opinau/cv-2/modul 1 - openmv/Dokumentacija/images_sa_artifektima_cons_level/slika_1_off.bmp

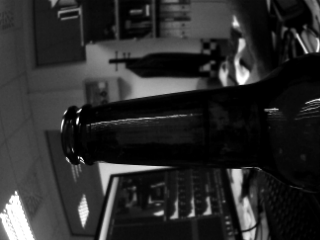
modul 1 - openmv/Dokumentacija/images_sa_artifektima_cons_level/slika_1_off.bmp
