opinau/cv-2/modul 1 - openmv/Kodovi/kicad_nacrt/openmv_breakout/openmv_breakout.jpg

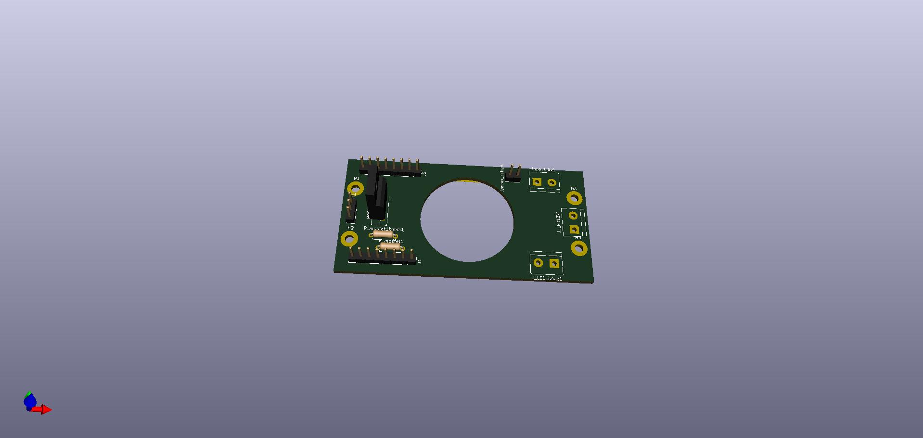
modul 1 - openmv/Kodovi/kicad_nacrt/openmv_breakout/openmv_breakout.jpg
