opinau/cv-2/modul 2 - rpi/Dokumentacija/last_frame.jpg

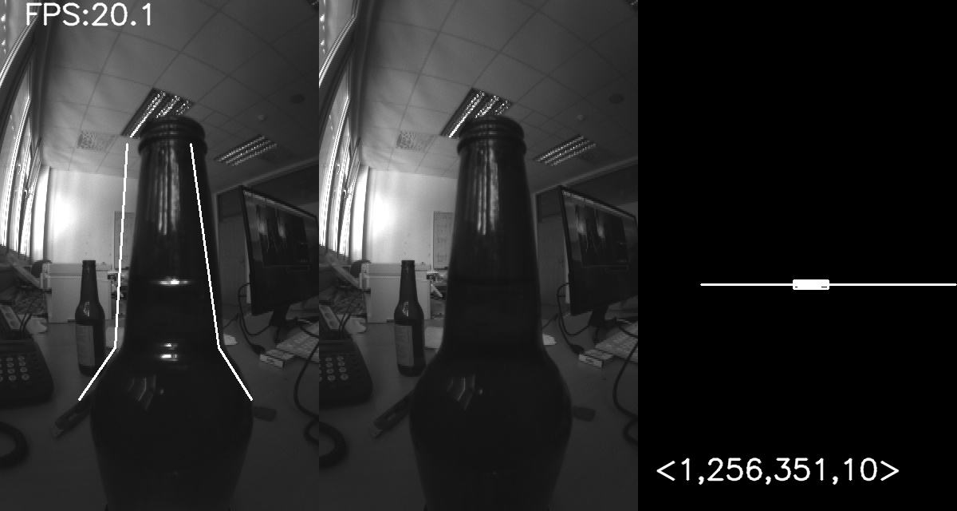
modul 2 - rpi/Dokumentacija/last_frame.jpg
