opinau/cv-2/modul 2 - rpi/Kodovi/fill_level/maska_rpi.bmp

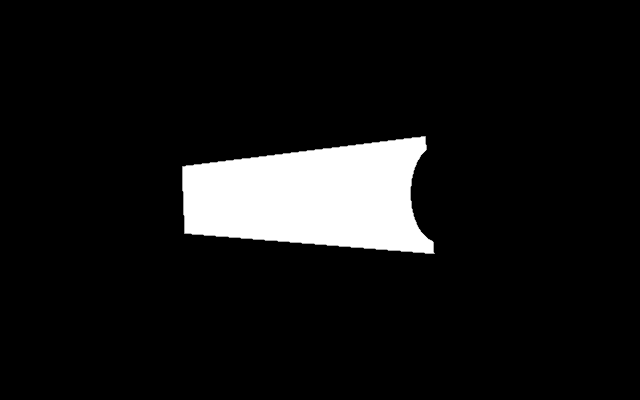
modul 2 - rpi/Kodovi/fill_level/maska_rpi.bmp
