opinau/cv-2/modul 2 - rpi/Kodovi/fill_level/slika_za_masku.bmp

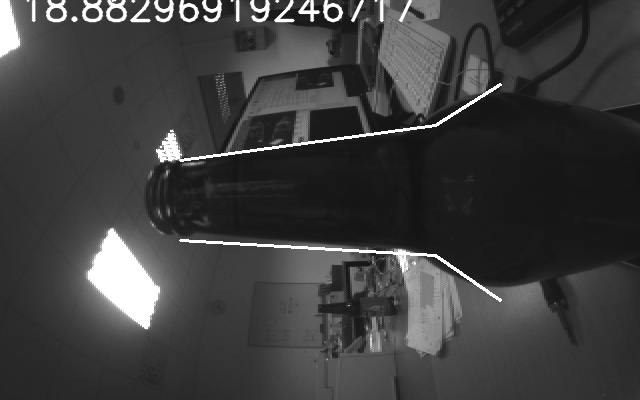
modul 2 - rpi/Kodovi/fill_level/slika_za_masku.bmp
