opinau/cv-2/modul 1 - openmv/Dokumentacija/test slike/slike diff 4 11 2021/diff_19.bmp

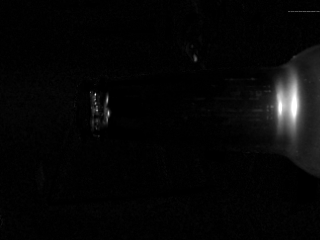
modul 1 - openmv/Dokumentacija/test slike/slike diff 4 11 2021/diff_19.bmp
