opinau/cv-2/modul 1 - openmv/Dokumentacija/test slike/slike diff 4 11 2021/slika_5_on.bmp

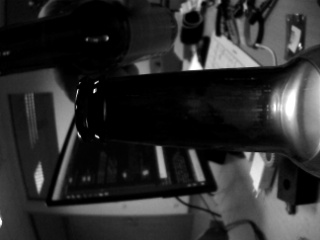
modul 1 - openmv/Dokumentacija/test slike/slike diff 4 11 2021/slika_5_on.bmp
