opinau/cv-2/modul 1 - openmv/Dokumentacija/test_slika_u_pivovari/slika_4_on.bmp

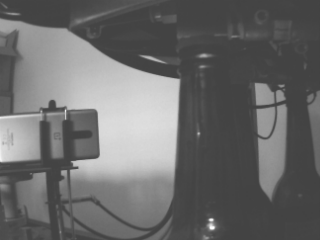
modul 1 - openmv/Dokumentacija/test_slika_u_pivovari/slika_4_on.bmp
