opinau/cv-2/modul 1 - openmv/Dokumentacija/test_slika_u_pivovari/slika_54_off.bmp

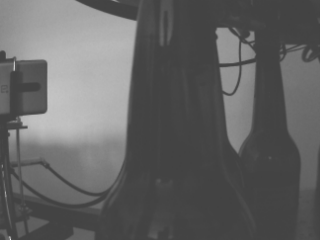
modul 1 - openmv/Dokumentacija/test_slika_u_pivovari/slika_54_off.bmp
